AlexKozllov/HyperCube_Evolution/images/1b4beea023ea96fc2a2bd98361bb5665_preview_featured.jpg

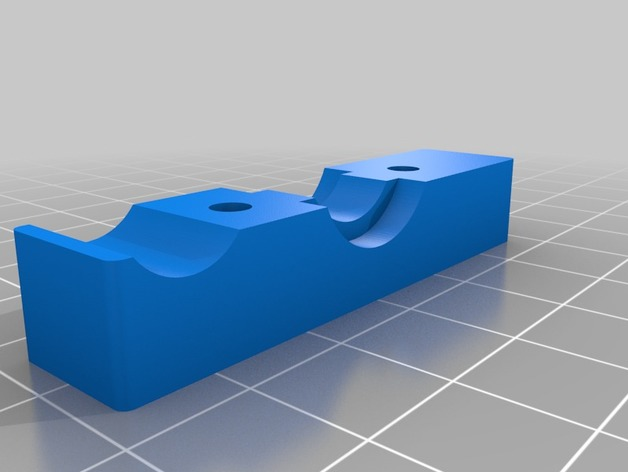
images/1b4beea023ea96fc2a2bd98361bb5665_preview_featured.jpg
