AlexKozllov/HyperCube_Evolution/images/1d4d6eae774d4cb255d003c31bb768ba_preview_featured.jpg

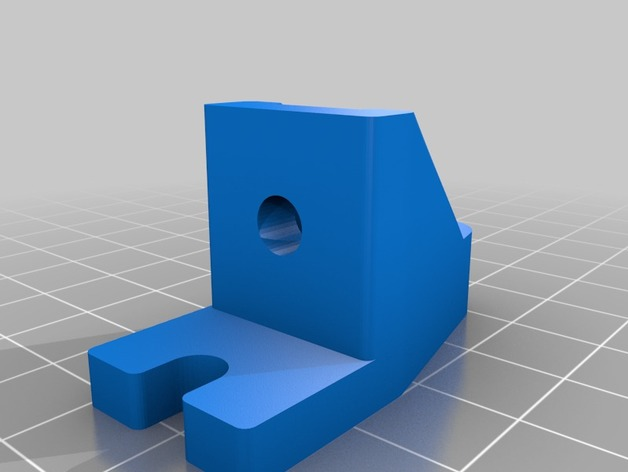
images/1d4d6eae774d4cb255d003c31bb768ba_preview_featured.jpg
