AlexKozllov/HyperCube_Evolution/images/03bf15b9146628fa0817c1cd7abfff11_preview_featured.jpg

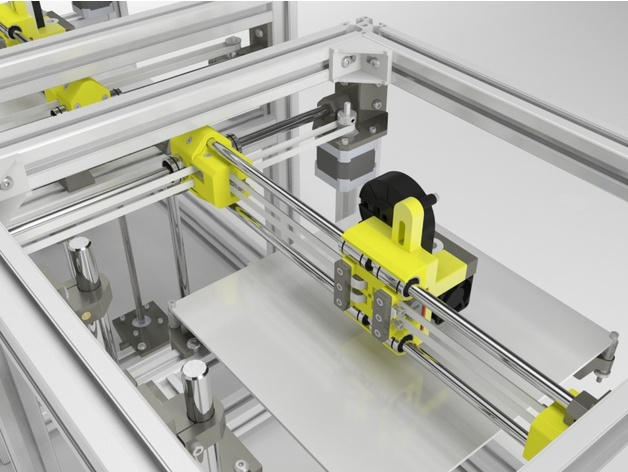
images/03bf15b9146628fa0817c1cd7abfff11_preview_featured.jpg
