AlexKozllov/HyperCube_Evolution/images/3db99d4a36ee1cc795951ca50e5e4f23_preview_featured.jpg

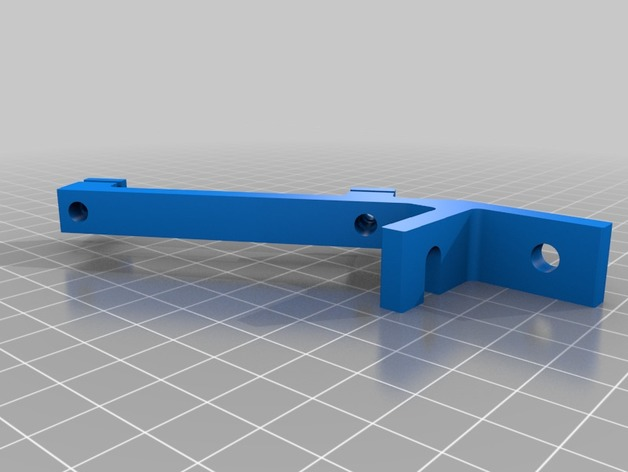
images/3db99d4a36ee1cc795951ca50e5e4f23_preview_featured.jpg
