AlexKozllov/HyperCube_Evolution/images/05b6e174447ac4267728df5cdc1aa3c8_preview_featured.jpg

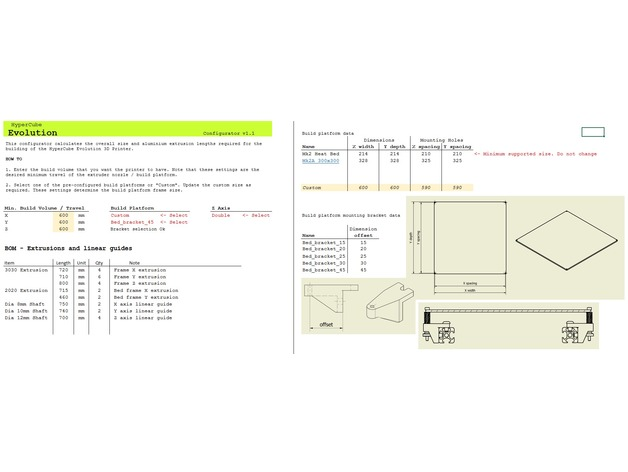
images/05b6e174447ac4267728df5cdc1aa3c8_preview_featured.jpg
