AlexKozllov/HyperCube_Evolution/images/5c4d1c6a0f745a4a3d2b838855627f32_preview_featured.jpg

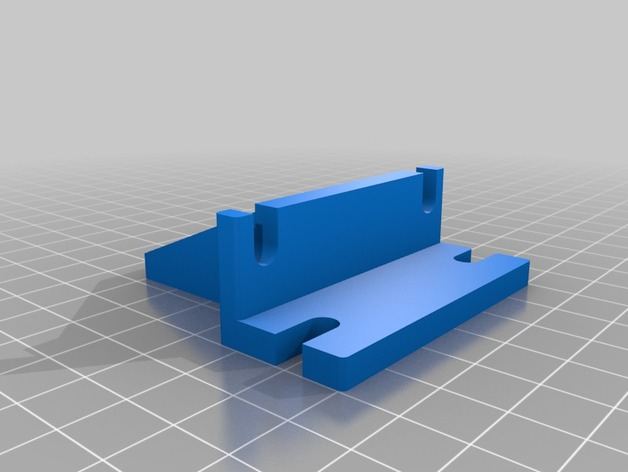
images/5c4d1c6a0f745a4a3d2b838855627f32_preview_featured.jpg
