AlexKozllov/HyperCube_Evolution/images/7e087c0cf43365423a80c0332dca7e6a_preview_featured.jpg

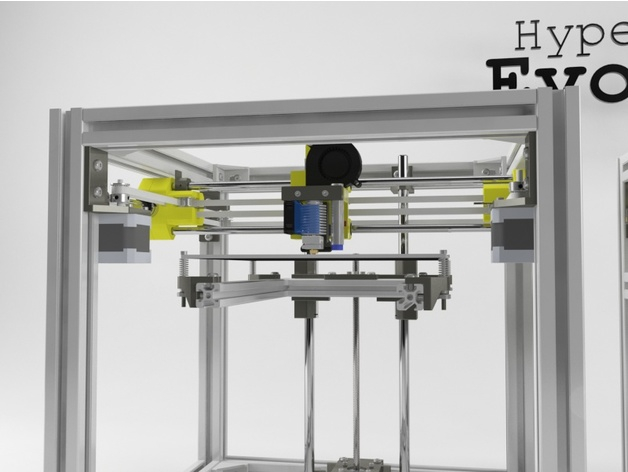
images/7e087c0cf43365423a80c0332dca7e6a_preview_featured.jpg
