AlexKozllov/HyperCube_Evolution/images/011c68071b331f977df2a17a48bdce89_preview_featured.jpg

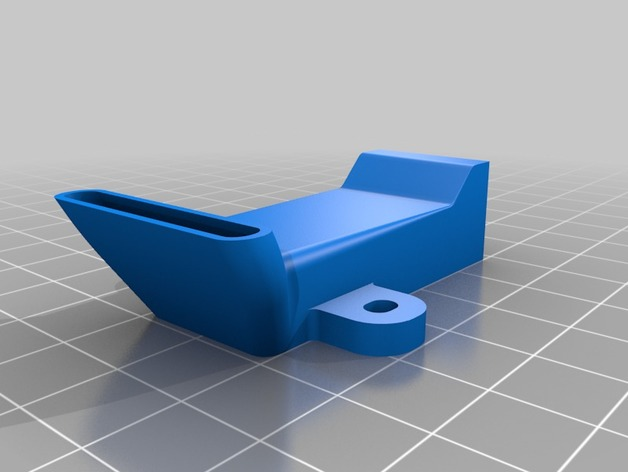
images/011c68071b331f977df2a17a48bdce89_preview_featured.jpg
