AlexKozllov/HyperCube_Evolution/images/13e88720b0addd61a31184d014ea6202_preview_featured.jpg

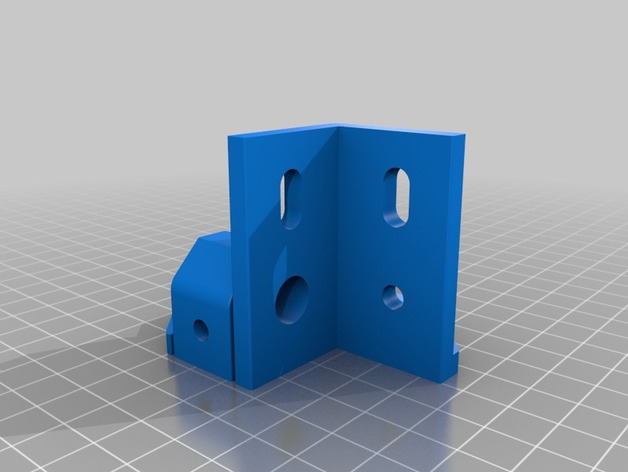
images/13e88720b0addd61a31184d014ea6202_preview_featured.jpg
