AlexKozllov/HyperCube_Evolution/images/35dae173d8318f3b2ba3616883fa8d4a_preview_featured.jpg

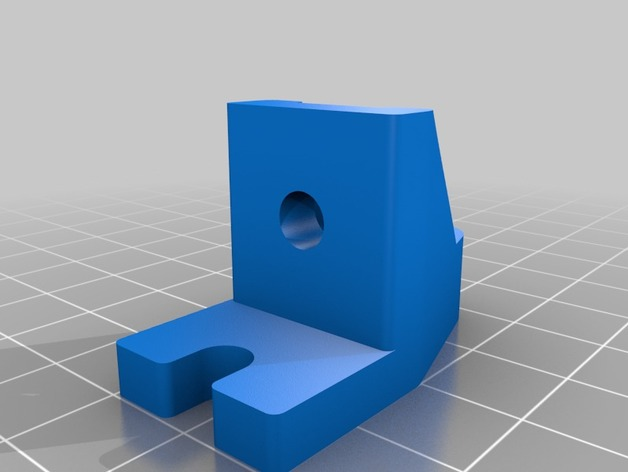
images/35dae173d8318f3b2ba3616883fa8d4a_preview_featured.jpg
