AlexKozllov/HyperCube_Evolution/images/55de20ed3f4ed6d7000a84408a9ab3df_preview_featured.jpg

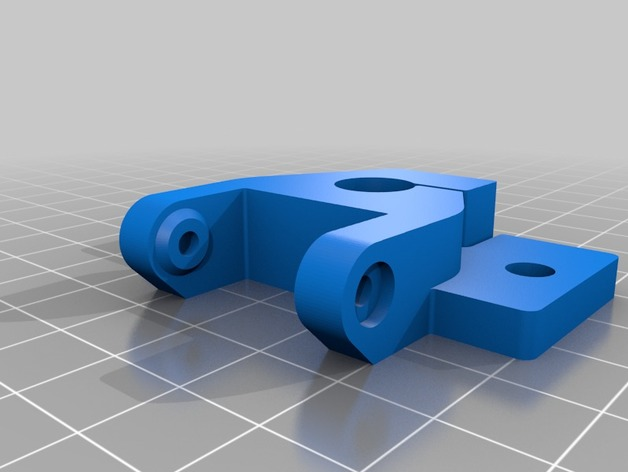
images/55de20ed3f4ed6d7000a84408a9ab3df_preview_featured.jpg
