AlexKozllov/HyperCube_Evolution/images/76ee36a6532162010765a9cd5dfdf645_preview_featured.jpg

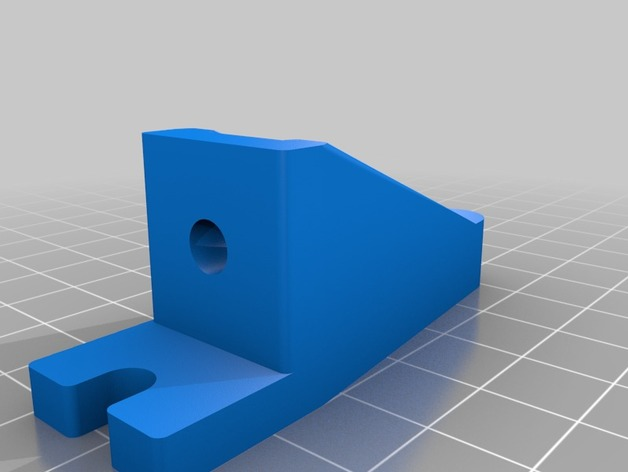
images/76ee36a6532162010765a9cd5dfdf645_preview_featured.jpg
