AlexKozllov/HyperCube_Evolution/images/86e2c8a223fce3331b4228fe11df1d3b_preview_featured.jpg

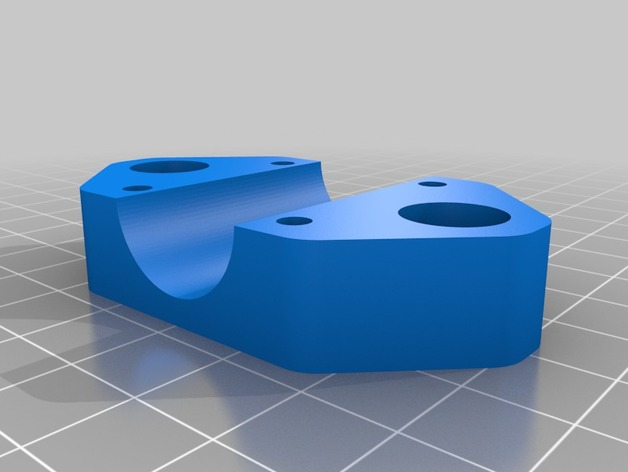
images/86e2c8a223fce3331b4228fe11df1d3b_preview_featured.jpg
