AlexKozllov/HyperCube_Evolution/images/95c8f065662b7c5c87987e73ba1b99e9_preview_featured.jpg

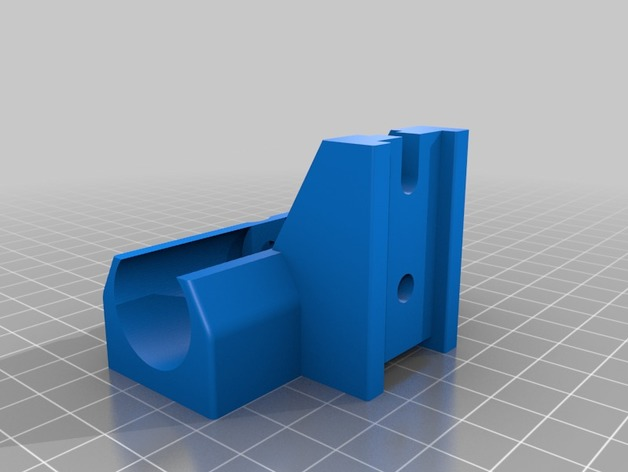
images/95c8f065662b7c5c87987e73ba1b99e9_preview_featured.jpg
