AlexKozllov/HyperCube_Evolution/images/483e008b760de8bda4a408111570a563_preview_featured.jpg

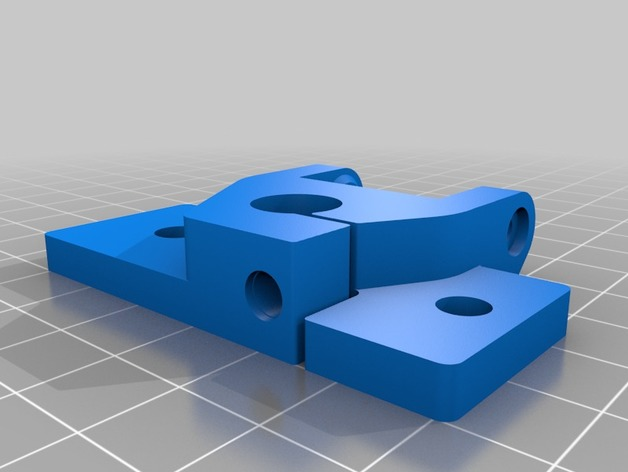
images/483e008b760de8bda4a408111570a563_preview_featured.jpg
