AlexKozllov/HyperCube_Evolution/images/486b5a0d39d0ece36f6778ba4687b5d9_preview_featured.JPG

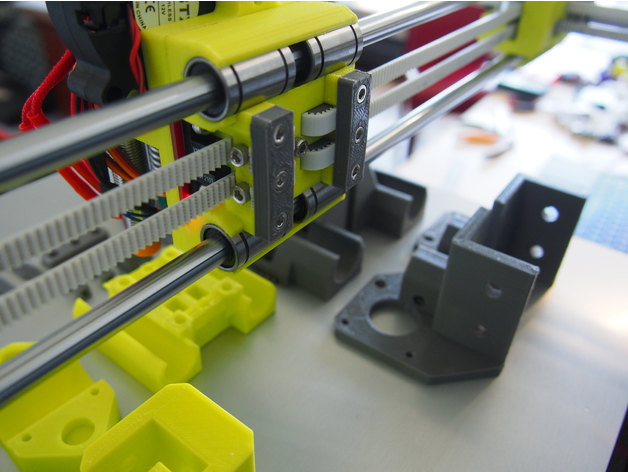
images/486b5a0d39d0ece36f6778ba4687b5d9_preview_featured.JPG
