AlexKozllov/HyperCube_Evolution/images/759ffed6b43b5e224f0fe2f2056089f3_preview_featured.jpg

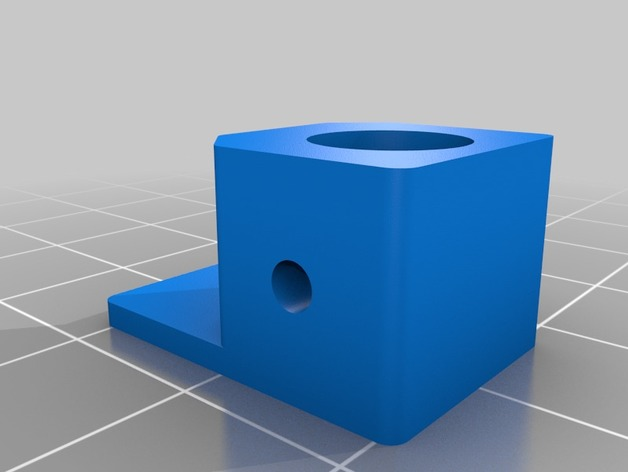
images/759ffed6b43b5e224f0fe2f2056089f3_preview_featured.jpg
