AlexKozllov/HyperCube_Evolution/images/765cebe16d591c7aa406e9e28d8711b6_preview_featured.jpg

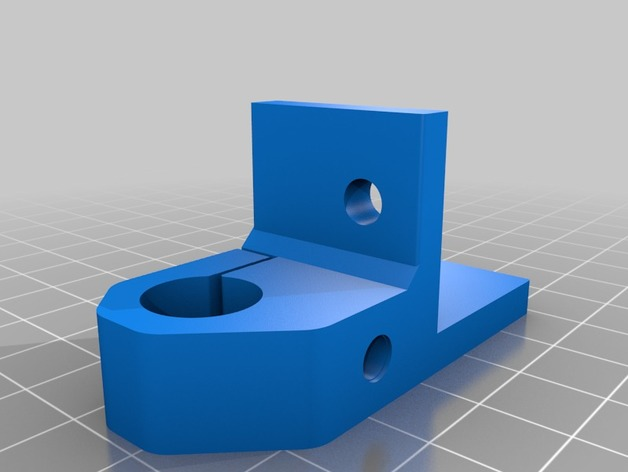
images/765cebe16d591c7aa406e9e28d8711b6_preview_featured.jpg
