AlexKozllov/HyperCube_Evolution/images/909c2d6a89dfd2d070b8082f0f9ae6f5_preview_featured.jpg

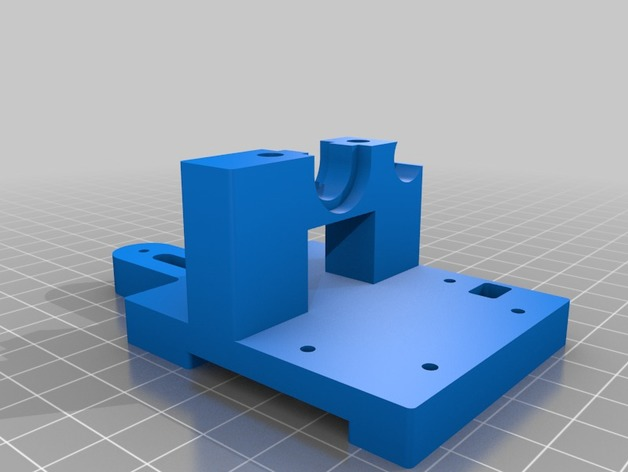
images/909c2d6a89dfd2d070b8082f0f9ae6f5_preview_featured.jpg
