AlexKozllov/HyperCube_Evolution/images/917ea9e382b296b37703f7a1b258a298_preview_featured.jpg

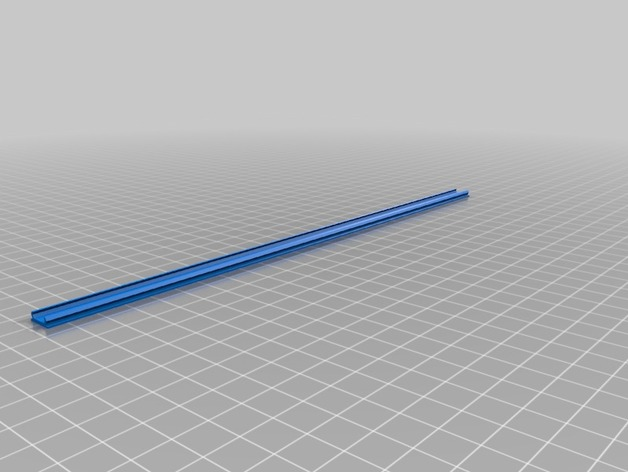
images/917ea9e382b296b37703f7a1b258a298_preview_featured.jpg
