AlexKozllov/HyperCube_Evolution/images/70625e6256f21bbbd93939ddc3c3ec53_preview_featured.jpg

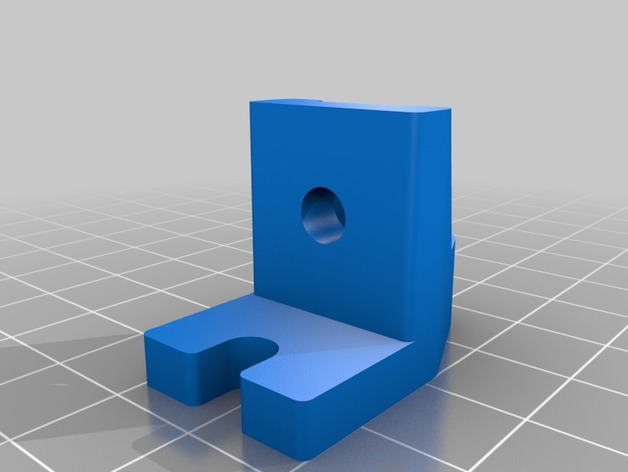
images/70625e6256f21bbbd93939ddc3c3ec53_preview_featured.jpg
