AlexKozllov/HyperCube_Evolution/images/321182c11e3212dc8e0e69a5f3e3804d_preview_featured.jpg

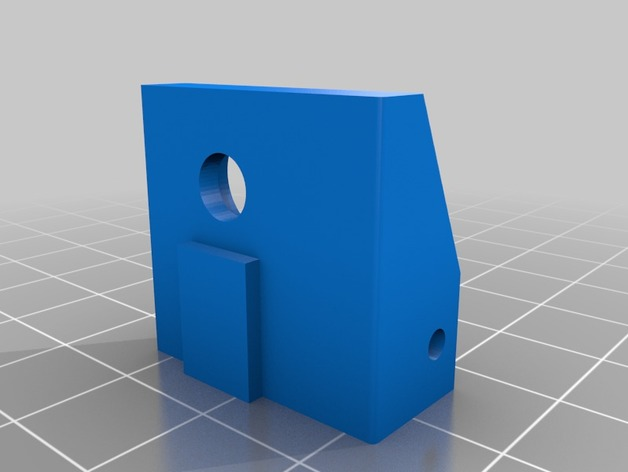
images/321182c11e3212dc8e0e69a5f3e3804d_preview_featured.jpg
