AlexKozllov/HyperCube_Evolution/images/440403ffef4816189c7463f7ed23ee38_preview_featured.jpg

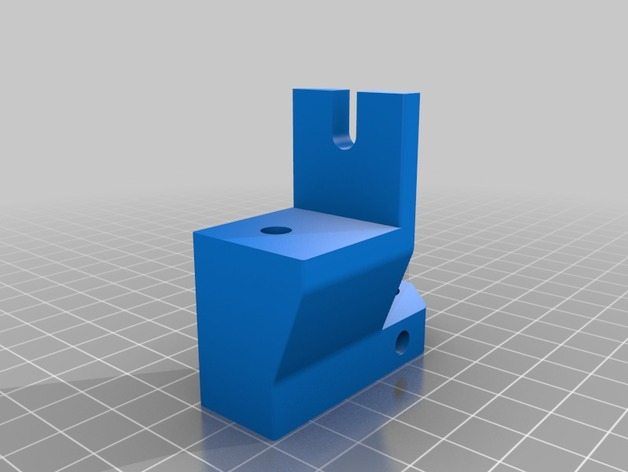
images/440403ffef4816189c7463f7ed23ee38_preview_featured.jpg
