AlexKozllov/HyperCube_Evolution/images/595788a016c84cb28e6fd6226ec65d3a_preview_featured.jpg

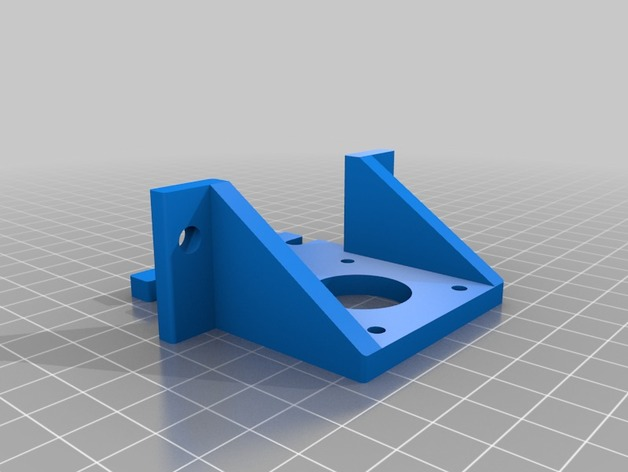
images/595788a016c84cb28e6fd6226ec65d3a_preview_featured.jpg
