AlexKozllov/HyperCube_Evolution/images/059110152a21718985263b7ea9c0bcb0_preview_featured.jpg

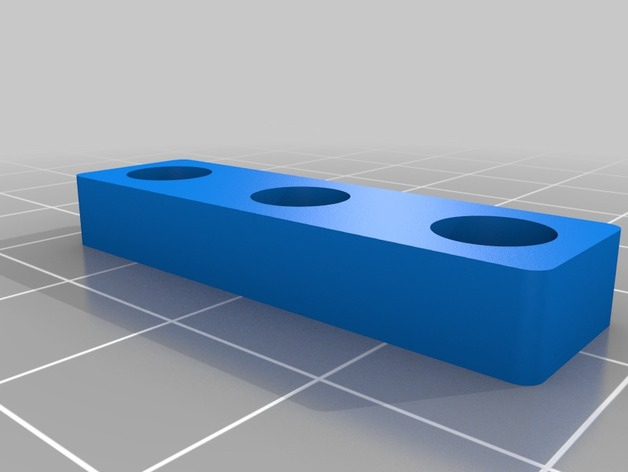
images/059110152a21718985263b7ea9c0bcb0_preview_featured.jpg
