AlexKozllov/HyperCube_Evolution/images/8676773706e0719136a0917f31ae14ea_preview_featured.JPG

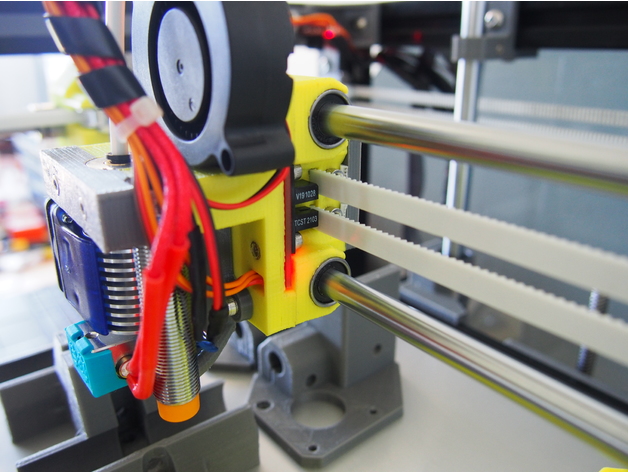
images/8676773706e0719136a0917f31ae14ea_preview_featured.JPG
