AlexKozllov/HyperCube_Evolution/images/b8b0900835846ce02f2ad12f02fc3c08_preview_featured.jpg

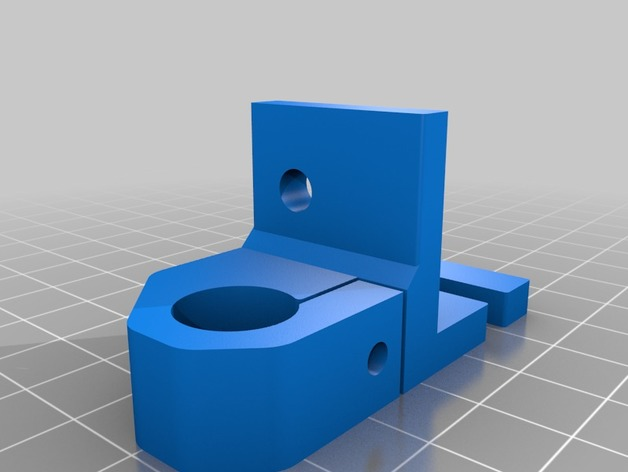
images/b8b0900835846ce02f2ad12f02fc3c08_preview_featured.jpg
