AlexKozllov/HyperCube_Evolution/images/b70cdbfc07a853387f34afb5264f7955_preview_featured.jpg

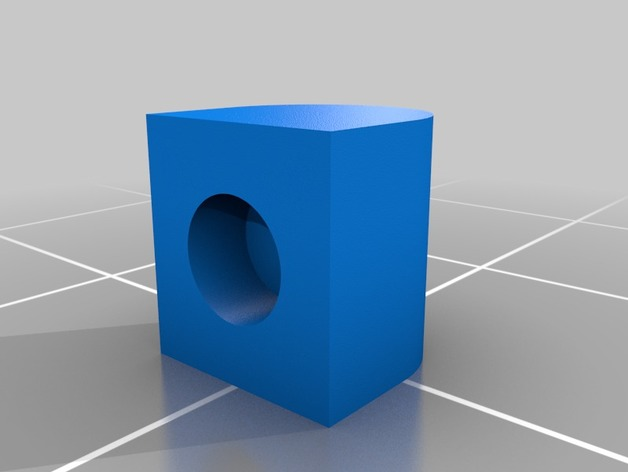
images/b70cdbfc07a853387f34afb5264f7955_preview_featured.jpg
