AlexKozllov/HyperCube_Evolution/images/ba8b123e2a5eb50a82a4163fbd6c87ee_preview_featured.JPG

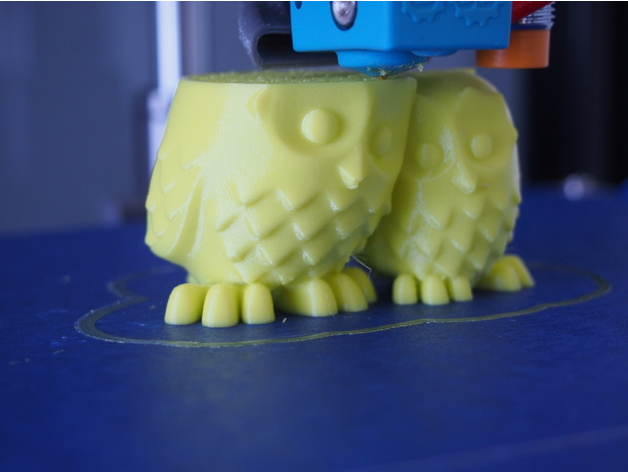
images/ba8b123e2a5eb50a82a4163fbd6c87ee_preview_featured.JPG
