AlexKozllov/HyperCube_Evolution/images/c15a5d0a094eefbfd0777dcf760a8b9b_preview_featured.jpg

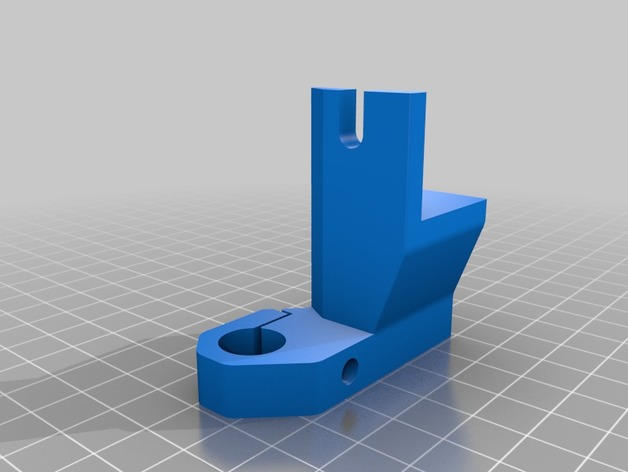
images/c15a5d0a094eefbfd0777dcf760a8b9b_preview_featured.jpg
