AlexKozllov/HyperCube_Evolution/images/ca38fe3fc9b49aebf15cef38d642ea8b_preview_featured.jpg

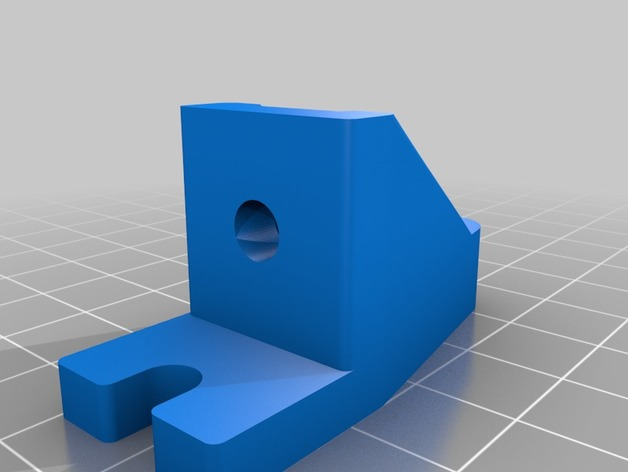
images/ca38fe3fc9b49aebf15cef38d642ea8b_preview_featured.jpg
