AlexKozllov/HyperCube_Evolution/images/d5755331a0203872a60ca0d3a213d13a_preview_featured.JPG

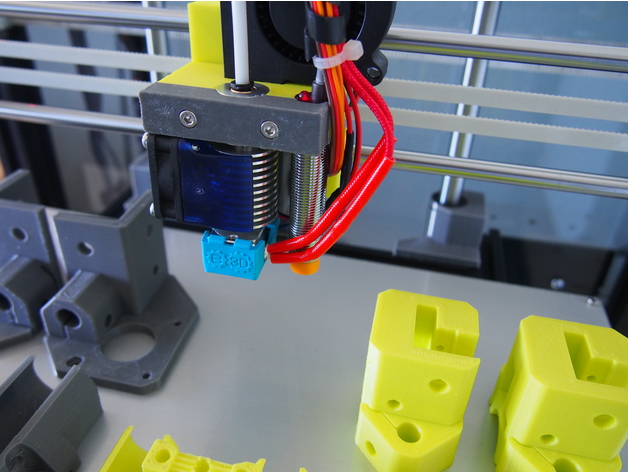
images/d5755331a0203872a60ca0d3a213d13a_preview_featured.JPG
