AlexKozllov/HyperCube_Evolution/images/dbfc8a5fbb18389d7925a4ed4eed3d0d_preview_featured.JPG

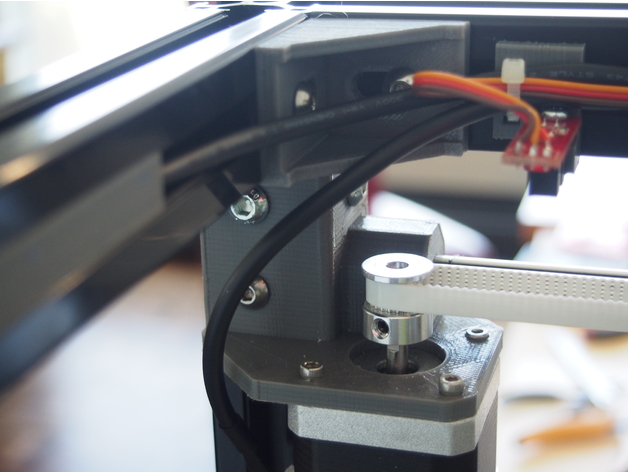
images/dbfc8a5fbb18389d7925a4ed4eed3d0d_preview_featured.JPG
