AlexKozllov/HyperCube_Evolution/images/e8b291c0265c24fa1ea8dc535c2fef1a_preview_featured.jpg

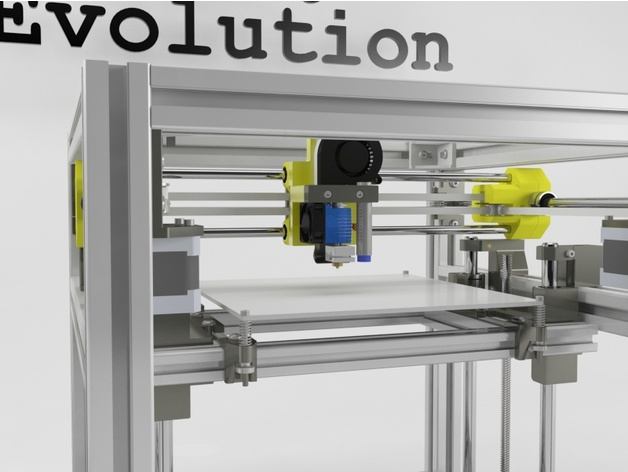
images/e8b291c0265c24fa1ea8dc535c2fef1a_preview_featured.jpg
