AlexKozllov/HyperCube_Evolution/images/e84a4715df7015fa97f11b3d1b9711fb_preview_featured.JPG

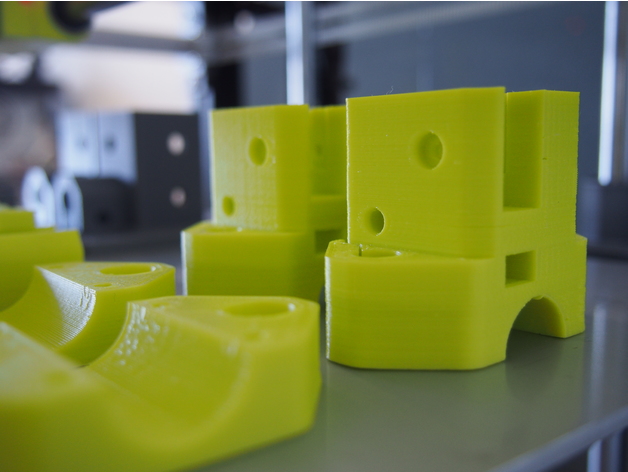
images/e84a4715df7015fa97f11b3d1b9711fb_preview_featured.JPG
