AlexKozllov/HyperCube_Evolution/images/e501fd2be94cc75ff6b52d71977eb82c_preview_featured.JPG

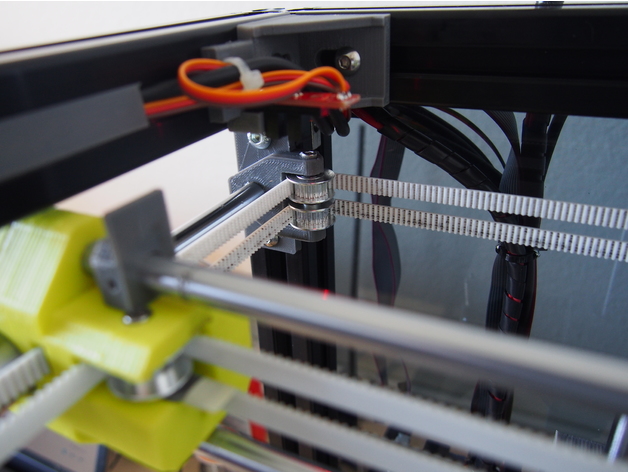
images/e501fd2be94cc75ff6b52d71977eb82c_preview_featured.JPG
