AlexKozllov/HyperCube_Evolution/images/e15019d2f73a920dc0173fe9b4fcd1bf_preview_featured.jpg

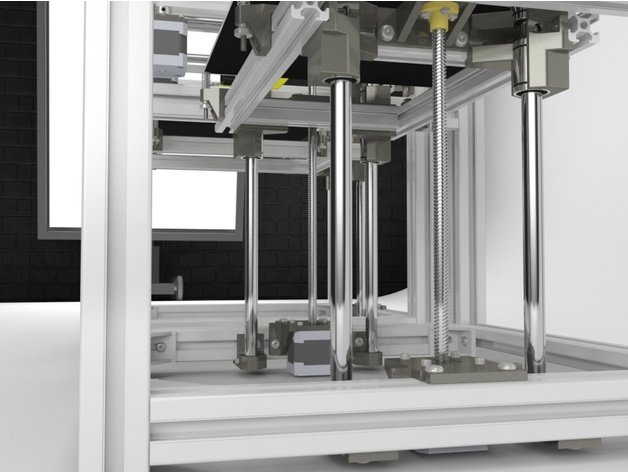
images/e15019d2f73a920dc0173fe9b4fcd1bf_preview_featured.jpg
