AlexKozllov/HyperCube_Evolution/images/e280975307c1c101063b3bd361d42cb4_preview_featured.jpg

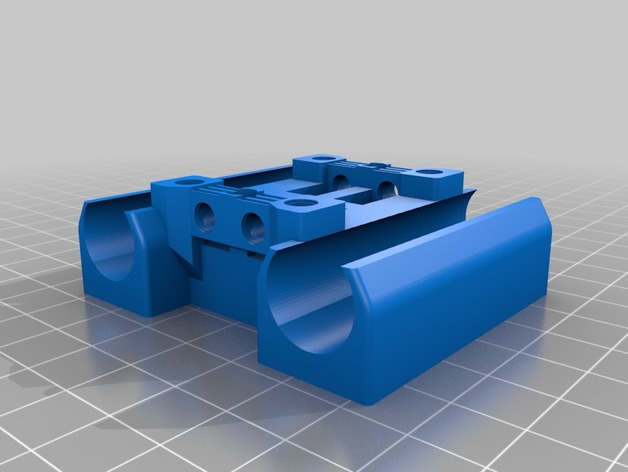
images/e280975307c1c101063b3bd361d42cb4_preview_featured.jpg
