AlexKozllov/HyperCube_Evolution/images/eef449a29611dfd0e3469d213acca68c_preview_featured.jpg

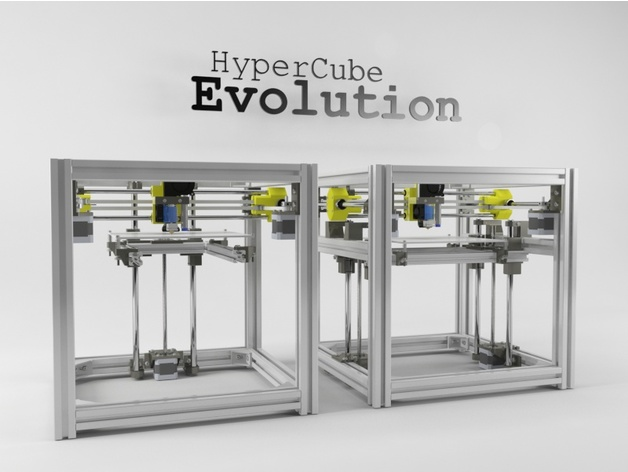
images/eef449a29611dfd0e3469d213acca68c_preview_featured.jpg
