AlexKozllov/HyperCube_Evolution/my_files/XY_Idler_Mount_-_Left_-_2.0.stl

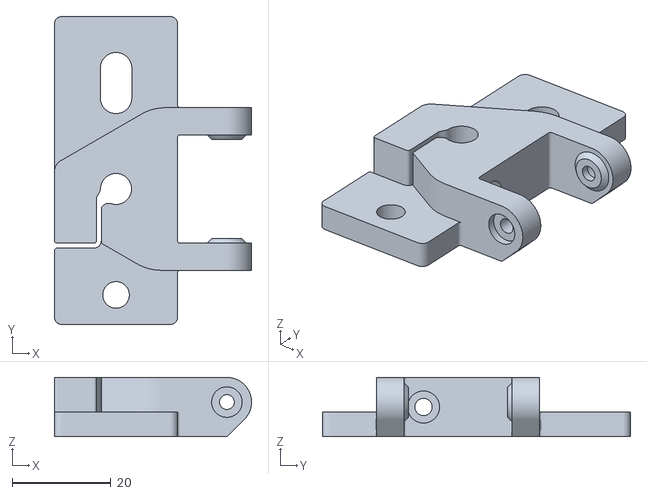
[picture p60: CAD file, 2020-06-09]
my_files/XY_Idler_Mount_-_Left_-_2.0.stl
40.0 x 62.5 x 12.0
