AlexKozllov/HyperCube_Evolution/my_files/my_XYZ_2_part/X_End_Stop_Flag_1.0.stl

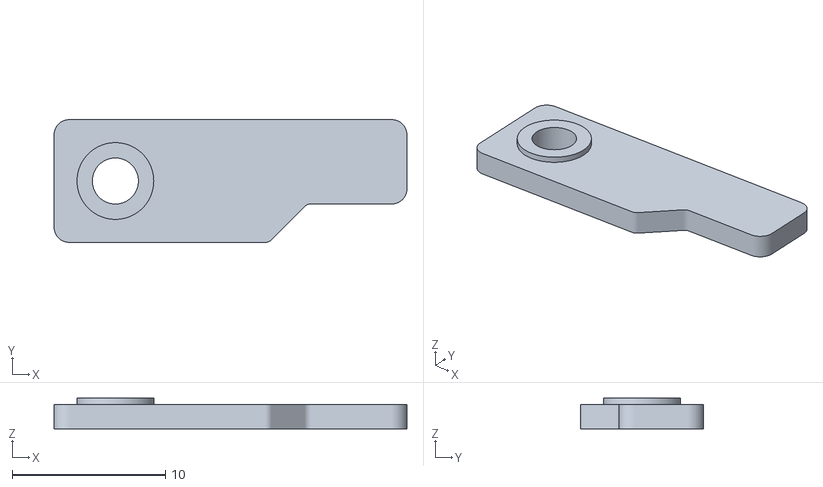
[picture p61: CAD file, 2020-06-09]
my_files/my_XYZ_2_part/X_End_Stop_Flag_1.0.stl
23.0 x 8.00 x 2.00
