AlexKozllov/HyperCube_Evolution/my_files/Y_Carriage_Clamp_LM8UU_2.0.stl

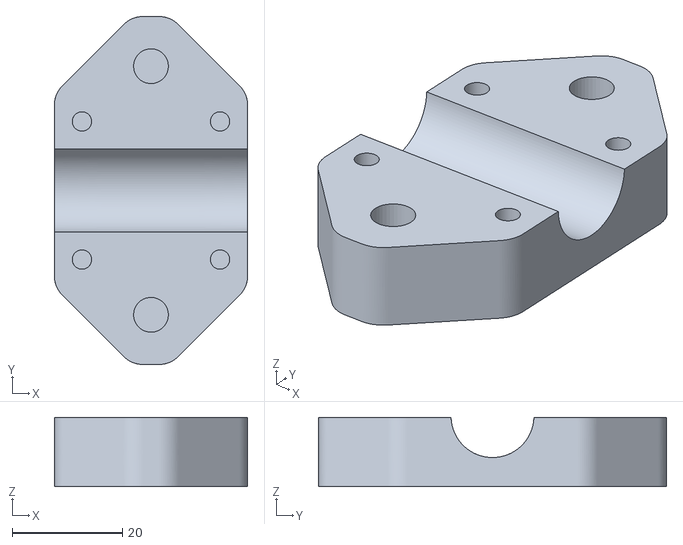
[picture p62: CAD file, 2020-06-09]
my_files/Y_Carriage_Clamp_LM8UU_2.0.stl
35.0 x 63.0 x 12.5
