AlexKozllov/HyperCube_Evolution/my_files/print_unchanged/FGSC_3030_Mount_-_Right_1.0.stl

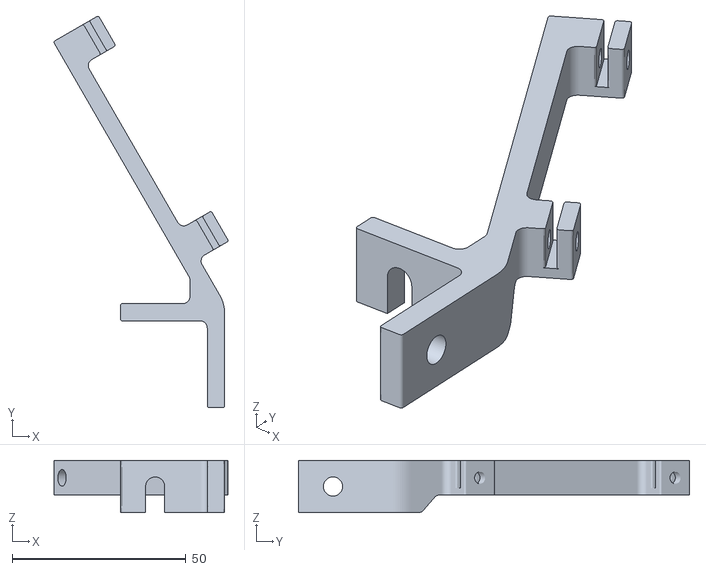
[picture p63: CAD file, 2020-06-09]
my_files/print_unchanged/FGSC_3030_Mount_-_Right_1.0.stl
50.1 x 112.8 x 15.0
