AlexKozllov/HyperCube_Evolution/files/Y_End_Stop_Bracket_1.0.stl

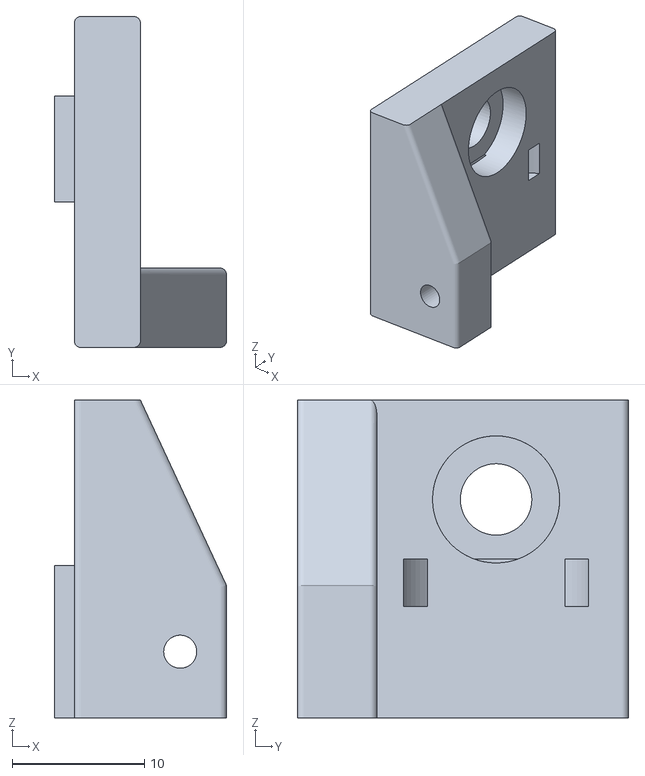
[picture p64: CAD file, 2020-06-09]
files/Y_End_Stop_Bracket_1.0.stl
13.0 x 25.0 x 24.0
