AlexKozllov/HyperCube_Evolution/my_files/print_unchanged/Retainer_1.0.stl

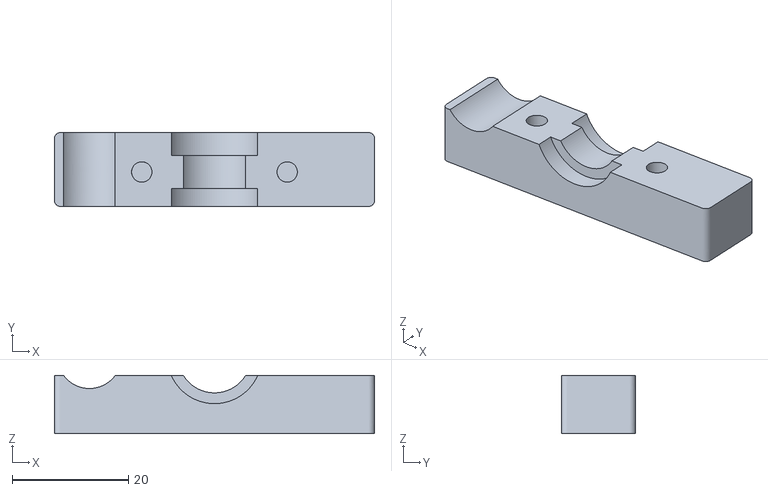
[picture p65: CAD file, 2020-06-09]
my_files/print_unchanged/Retainer_1.0.stl
55.0 x 12.7 x 10.0
