AlexKozllov/HyperCube_Evolution/files/Bed_Bracket_20_1.0.stl

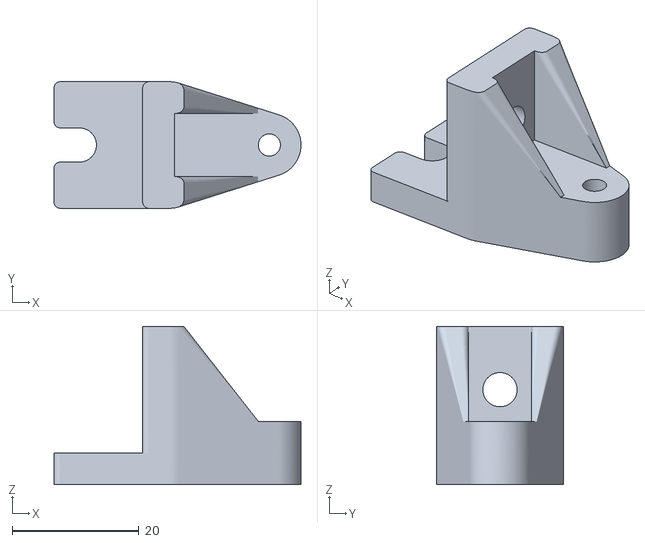
[picture p66: CAD file, 2020-06-09]
files/Bed_Bracket_20_1.0.stl
39.0 x 20.0 x 25.0
