AlexKozllov/HyperCube_Evolution/files/Bed_Bracket_40_1.0.stl

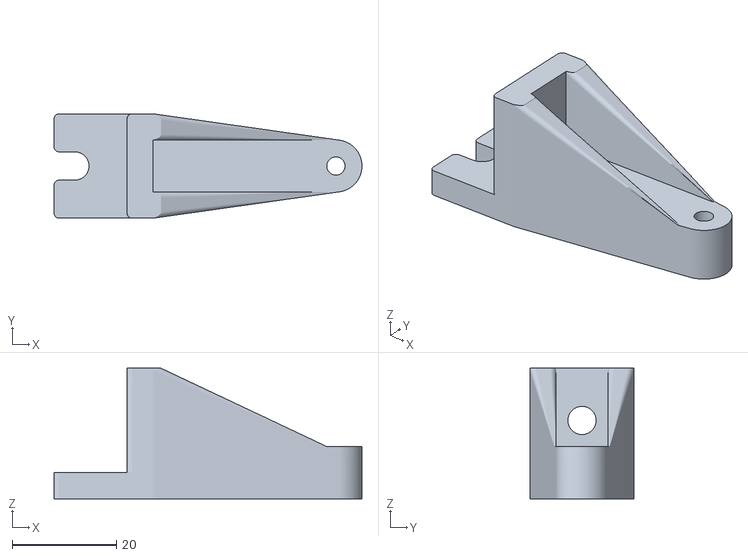
[picture p67: CAD file, 2020-06-09]
files/Bed_Bracket_40_1.0.stl
59.0 x 20.0 x 25.0
