AlexKozllov/HyperCube_Evolution/files/HyperCube_Logo.dxf

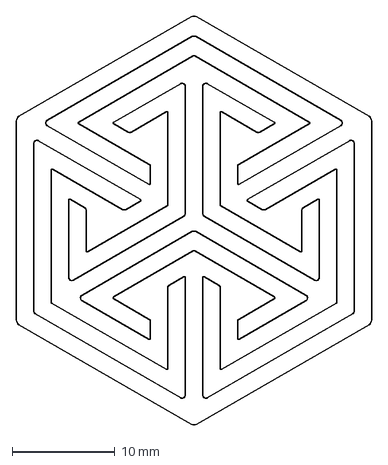
[picture p68: CAD file, 2020-06-09]
files/HyperCube_Logo.dxf
34.6 x 39.9 mm
