AlexKozllov/HyperCube_Evolution/files/Bed_Bracket_15_1.0.stl

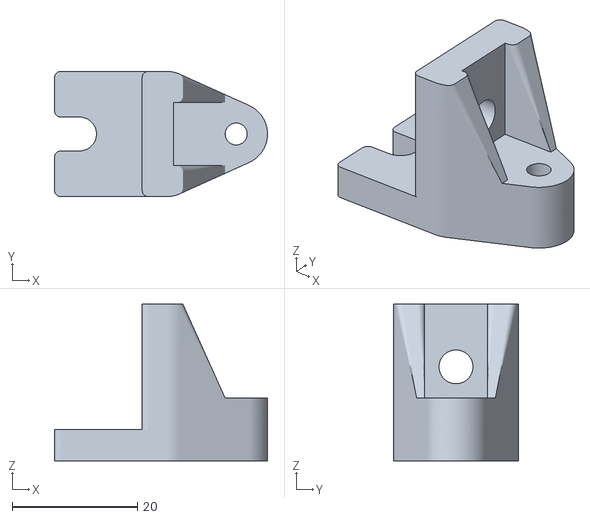
[picture p69: CAD file, 2020-06-09]
files/Bed_Bracket_15_1.0.stl
34.0 x 20.0 x 25.0
