AlexKozllov/HyperCube_Evolution/files/Z_Axis_Linear_Rail_Bracket_-_Double_Z_-_Right_1.1.stl

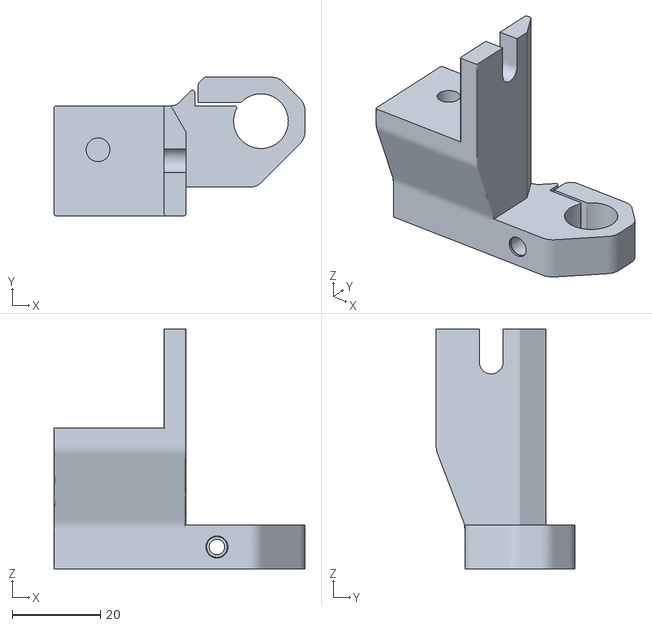
[picture p70: CAD file, 2020-06-09]
files/Z_Axis_Linear_Rail_Bracket_-_Double_Z_-_Right_1.1.stl
57.0 x 31.5 x 54.5
