AlexKozllov/HyperCube_Evolution/files/Y_Carriage_Clamp_LM8UU_1.0.stl

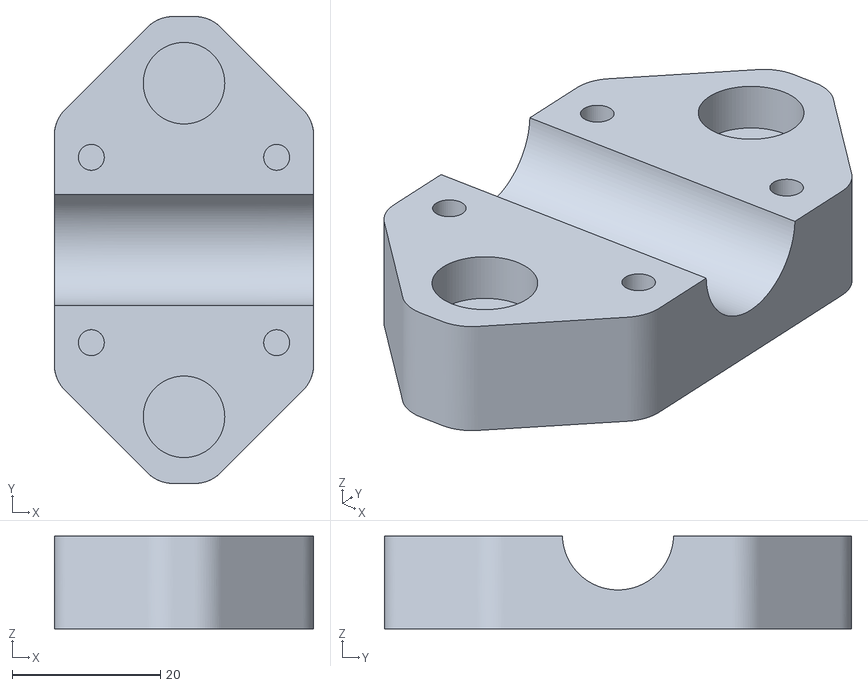
[picture p71: CAD file, 2020-06-09]
files/Y_Carriage_Clamp_LM8UU_1.0.stl
35.0 x 63.0 x 12.5
