AlexKozllov/HyperCube_Evolution/files/T_Slot_Cover_1.0_-_250mm.stl

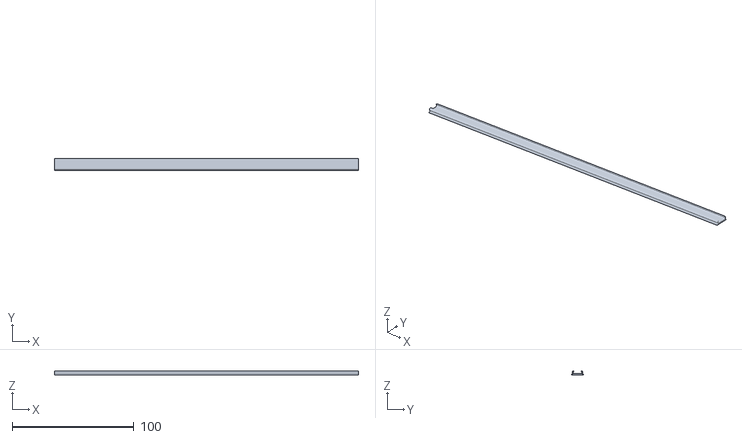
[picture p72: CAD file, 2020-06-09]
files/T_Slot_Cover_1.0_-_250mm.stl
250.0 x 9.80 x 3.20
