AlexKozllov/HyperCube_Evolution/files/Duct_1.0.stl

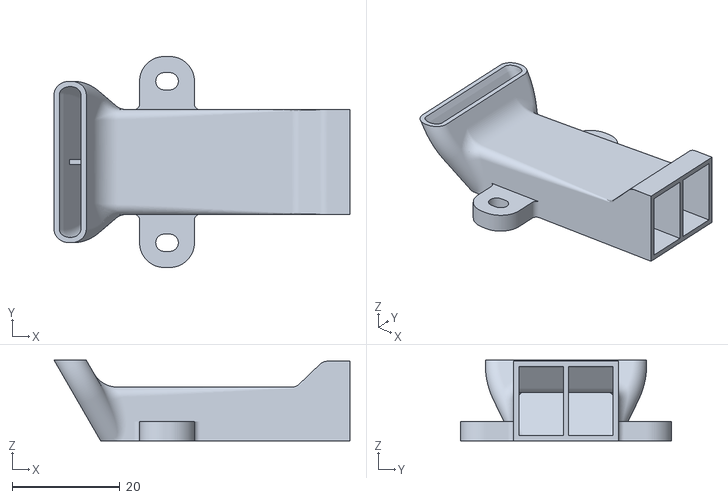
[picture p73: CAD file, 2020-06-09]
files/Duct_1.0.stl
55.0 x 39.2 x 15.0
