AlexKozllov/HyperCube_Evolution/files/Bed_Bracket_45_1.0.stl

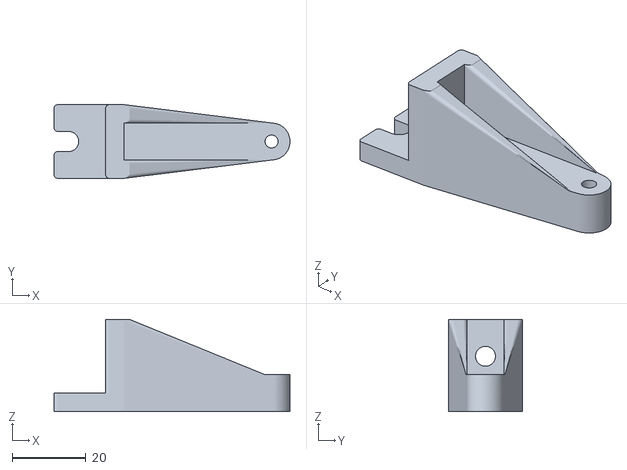
[picture p74: CAD file, 2020-06-09]
files/Bed_Bracket_45_1.0.stl
64.0 x 20.0 x 25.0
