AlexKozllov/HyperCube_Evolution/files/Y_Carriage_xDia10_LM8UU_1.0.stl

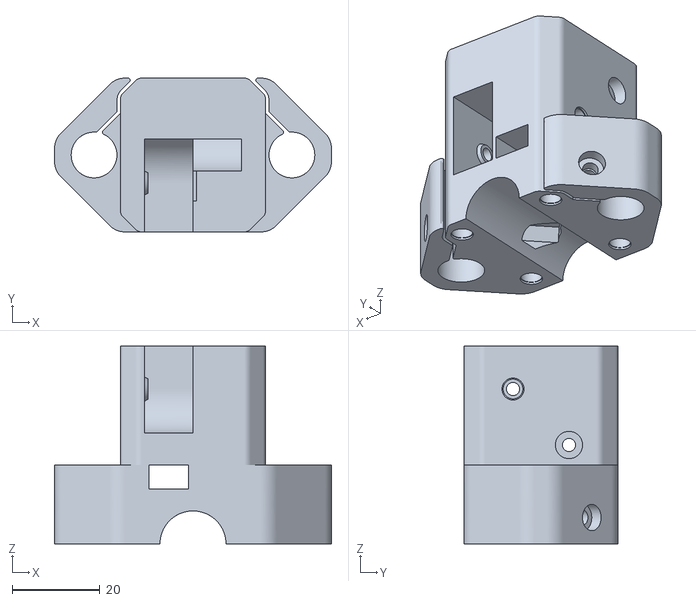
[picture p75: CAD file, 2020-06-09]
files/Y_Carriage_xDia10_LM8UU_1.0.stl
63.0 x 35.0 x 45.0
